HandHeldLegend/progcc-4-hw/3D/PCB/PGS_USBW_Board.step

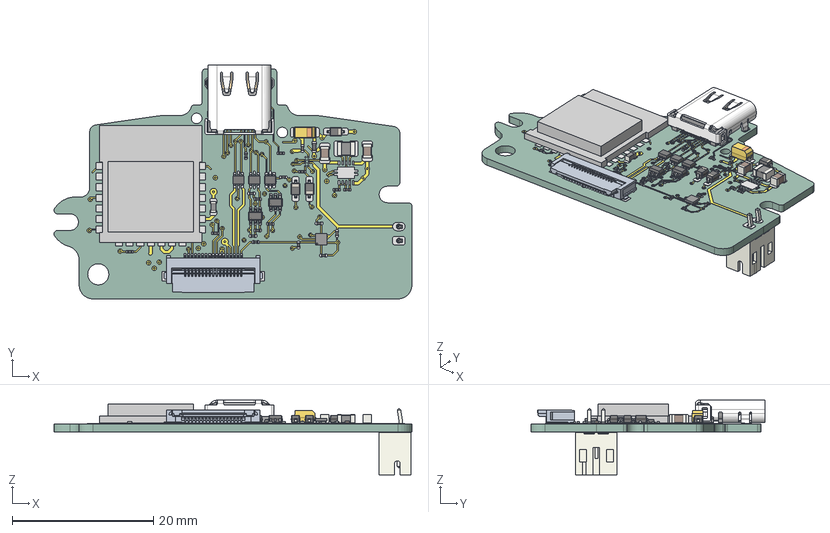
[picture p15: CAD file, 2026-09-22]
3D/PCB/PGS_USBW_Board.step
50.8 x 33.2 x 10.6 mm
R_0201_0603Metric x 15
RM2-Primitive v1
SOT-363_SC-70-6 x 2
L_0603_1608Metric
C_0805_2012Metric x 2
D_SOD-323 x 3
SOT_666 x 3
C_0201_0603Metric x 4
R_0402_1005Metric
L_1008_2520Metric
CP_EIA_3216_18_Kemet_A
JST_B2B_PH_K
PGS_USBW_Board_copper
PGS_USBW_Board_pad
PGS_USBW_Board_via
PGS_USBW_Board_PCB
