HandHeldLegend/progcc-4-hw/3D/STEP/Silicone DPad.step

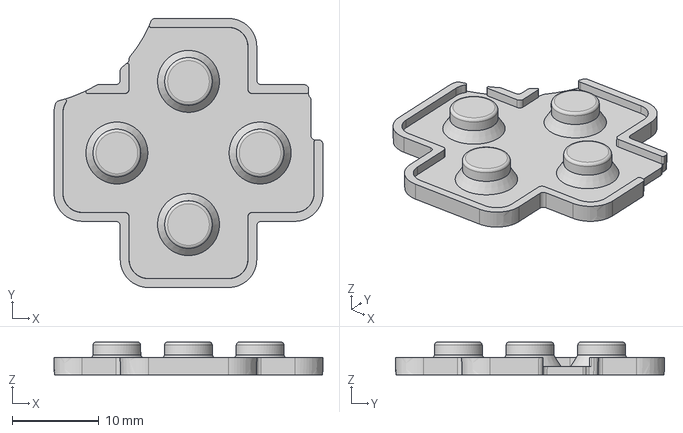
[picture p16: CAD file, 2026-09-22]
3D/STEP/Silicone DPad.step
31.0 x 31.0 x 3.80 mm
