HandHeldLegend/progcc-4-hw/3D/STL/DPad Body.stl

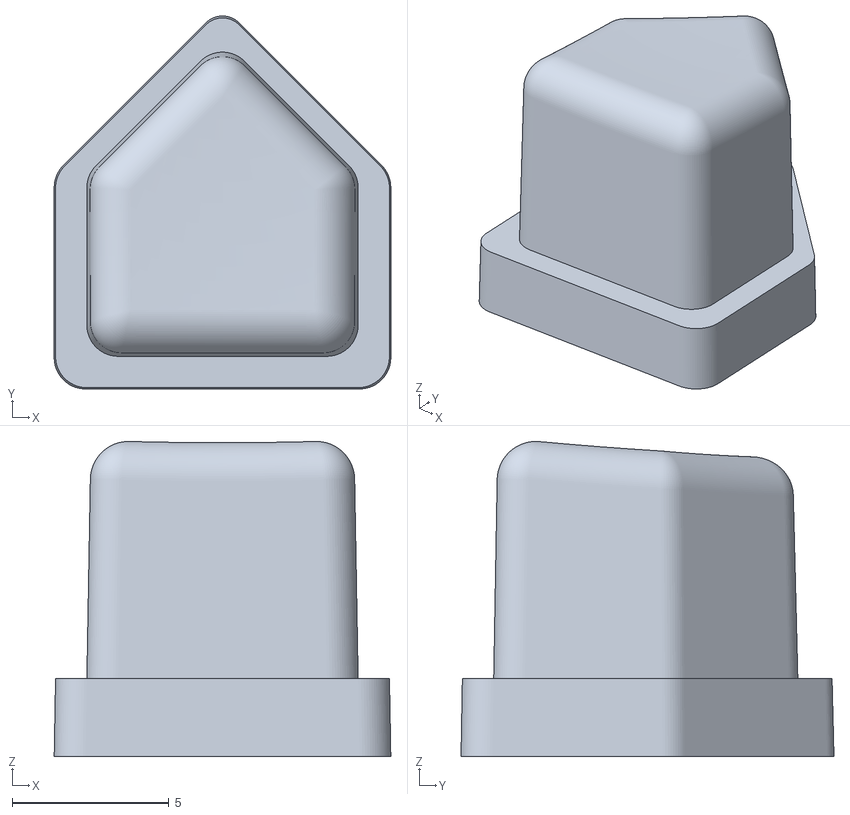
[picture p17: CAD file, 2026-09-25]
3D/STL/DPad Body.stl
10.8 x 11.9 x 10.1
