HandHeldLegend/progcc-4-hw/3D/STL/Button East Body.stl

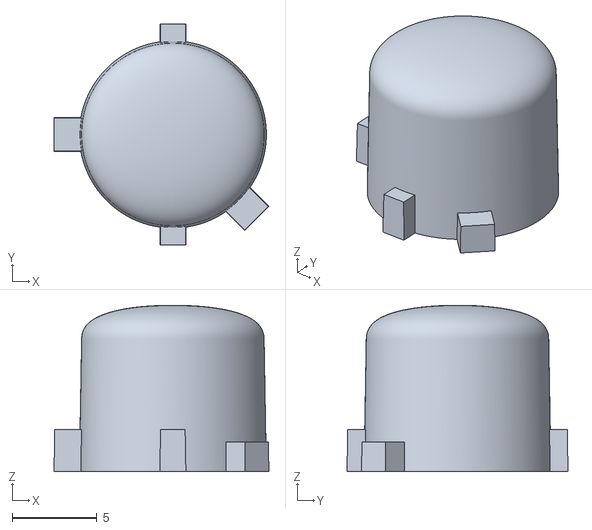
[picture p18: CAD file, 2026-09-25]
3D/STL/Button East Body.stl
12.7 x 13.0 x 9.82
