HandHeldLegend/progcc-4-hw/3D/STL/Triggers Body.stl

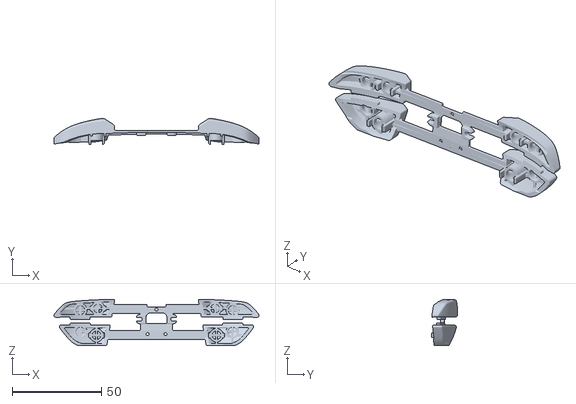
[picture p19: CAD file, 2026-09-25]
3D/STL/Triggers Body.stl
114.9 x 14.7 x 26.0
