HandHeldLegend/progcc-4-hw/PCB/Outlines/Trigger_Board_Export.dxf

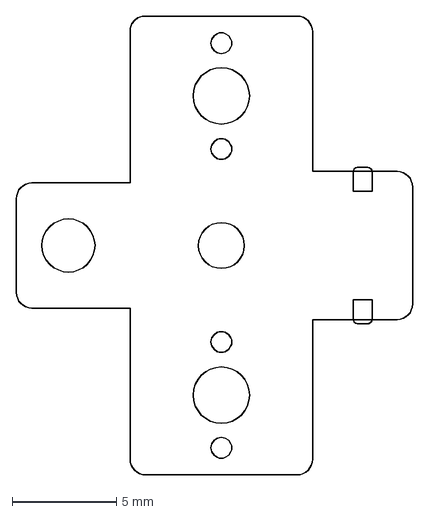
[picture p20: CAD file, 2025-05-15]
PCB/Outlines/Trigger_Board_Export.dxf
19.0 x 22.0 mm
