HandHeldLegend/progcc-4-hw/3D/STL/Player Lightpipe.stl

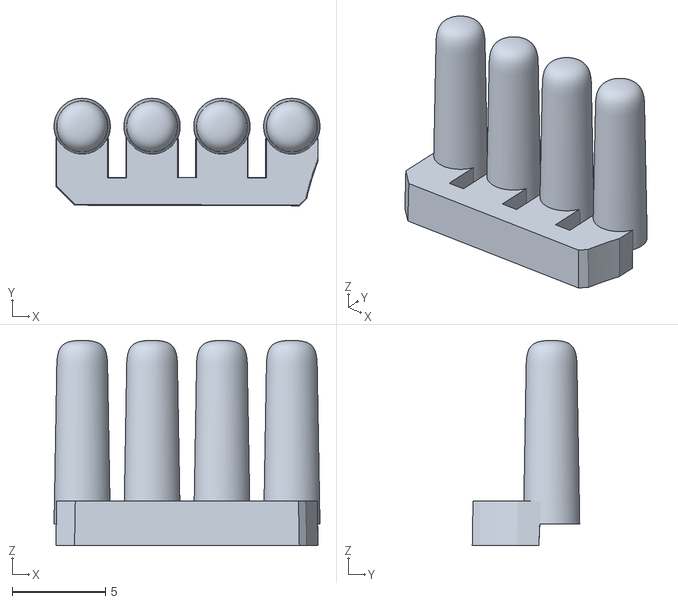
[picture p21: CAD file, 2026-09-22]
3D/STL/Player Lightpipe.stl
14.3 x 5.77 x 11.0
