HandHeldLegend/progcc-4-hw/PCB/Outlines/USB_Board_Export.dxf

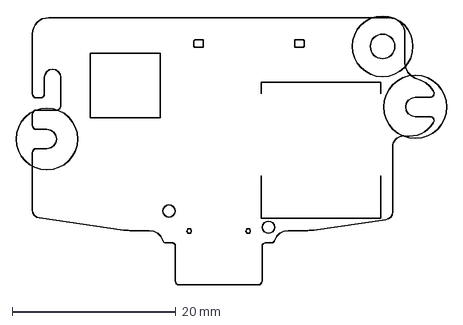
[picture p22: CAD file, 2025-05-15]
PCB/Outlines/USB_Board_Export.dxf
52.6 x 32.9 mm
