HandHeldLegend/progcc-4-hw/3D/STL/GL Button.stl

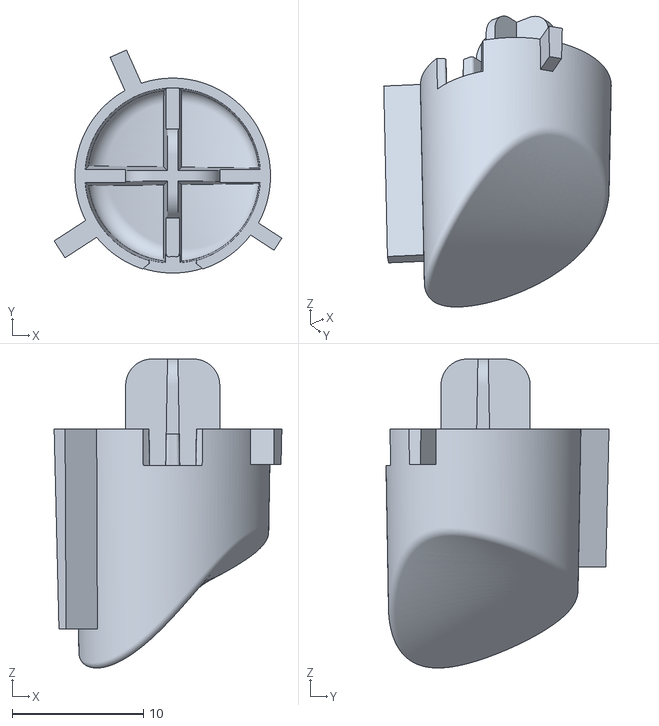
[picture p23: CAD file, 2026-09-22]
3D/STL/GL Button.stl
17.3 x 17.0 x 23.5
