HandHeldLegend/progcc-4-hw/PCB/Outlines/Stick_Module_Export.dxf

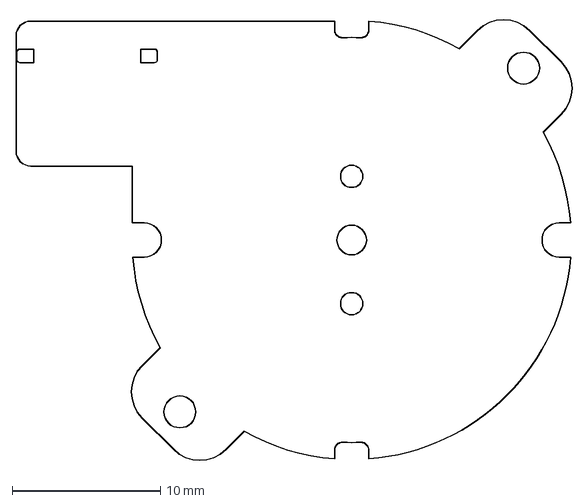
[picture p24: CAD file, 2025-05-15]
PCB/Outlines/Stick_Module_Export.dxf
37.5 x 30.2 mm
