HandHeldLegend/progcc-4-hw/3D/STL/Gateplate Round.stl

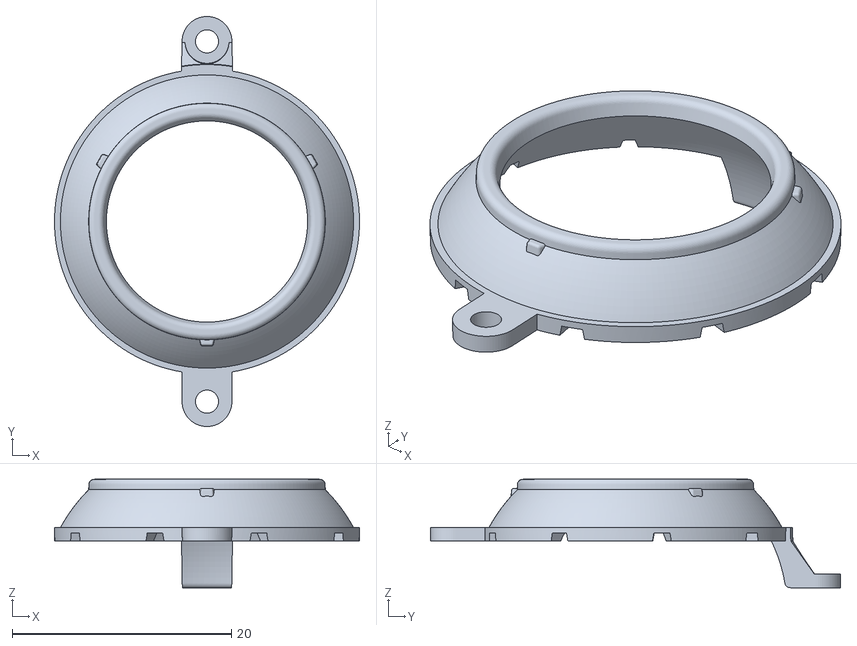
[picture p25: CAD file, 2026-09-22]
3D/STL/Gateplate Round.stl
27.8 x 37.4 x 9.89
