HandHeldLegend/progcc-4-hw/3D/STL/Shell Top Body.stl

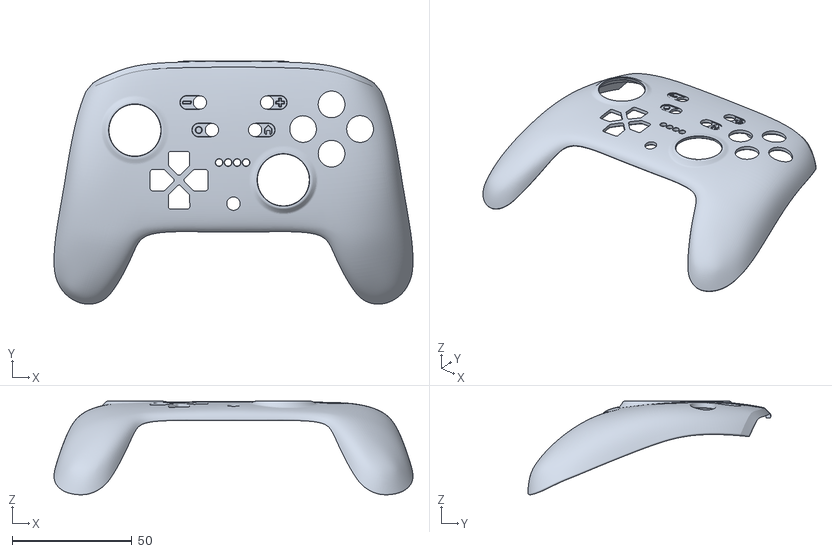
[picture p26: CAD file, 2026-09-22]
3D/STL/Shell Top Body.stl
150.0 x 101.7 x 39.1
