HandHeldLegend/progcc-4-hw/3D/STL/Shell Middle Body.stl

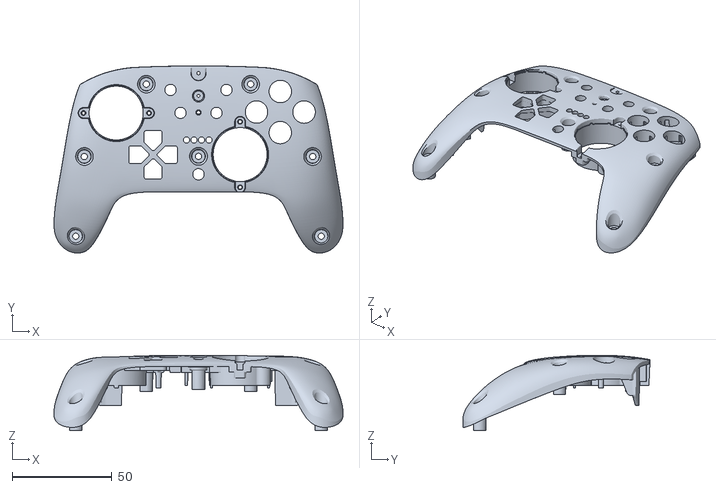
[picture p27: CAD file, 2026-09-22]
3D/STL/Shell Middle Body.stl
144.8 x 93.8 x 37.8
