HandHeldLegend/progcc-4-hw/3D/STL/Power Button.stl

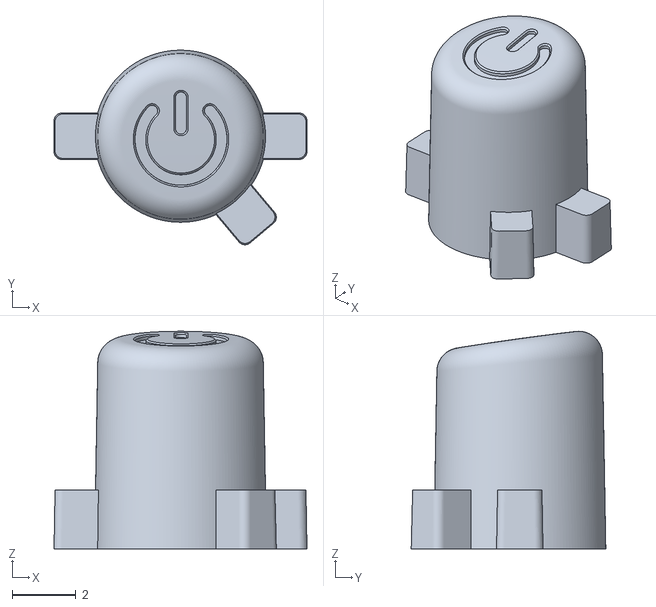
[picture p28: CAD file, 2026-09-22]
3D/STL/Power Button.stl
7.96 x 6.13 x 6.85
