HandHeldLegend/progcc-4-hw/3D/STL/Shell Lower Body.stl

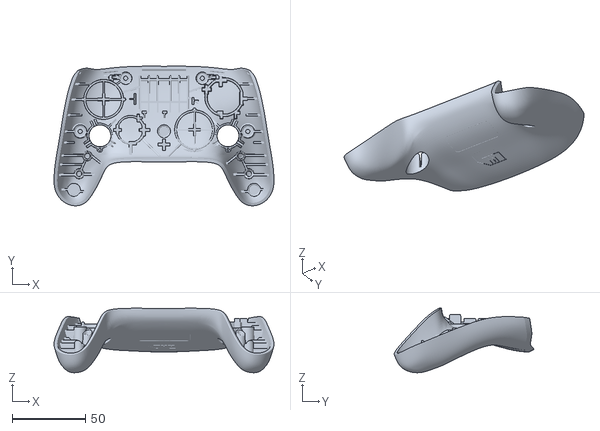
[picture p29: CAD file, 2026-09-22]
3D/STL/Shell Lower Body.stl
150.1 x 95.3 x 44.0
