HandHeldLegend/progcc-4-hw/3D/STL/Support Frame.stl

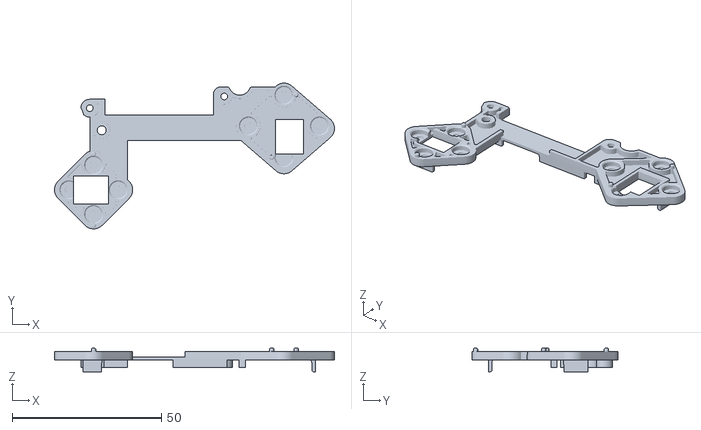
[picture p30: CAD file, 2026-09-22]
3D/STL/Support Frame.stl
93.7 x 48.8 x 7.89
