HandHeldLegend/progcc-4-hw/3D/STL/Menu Button.stl

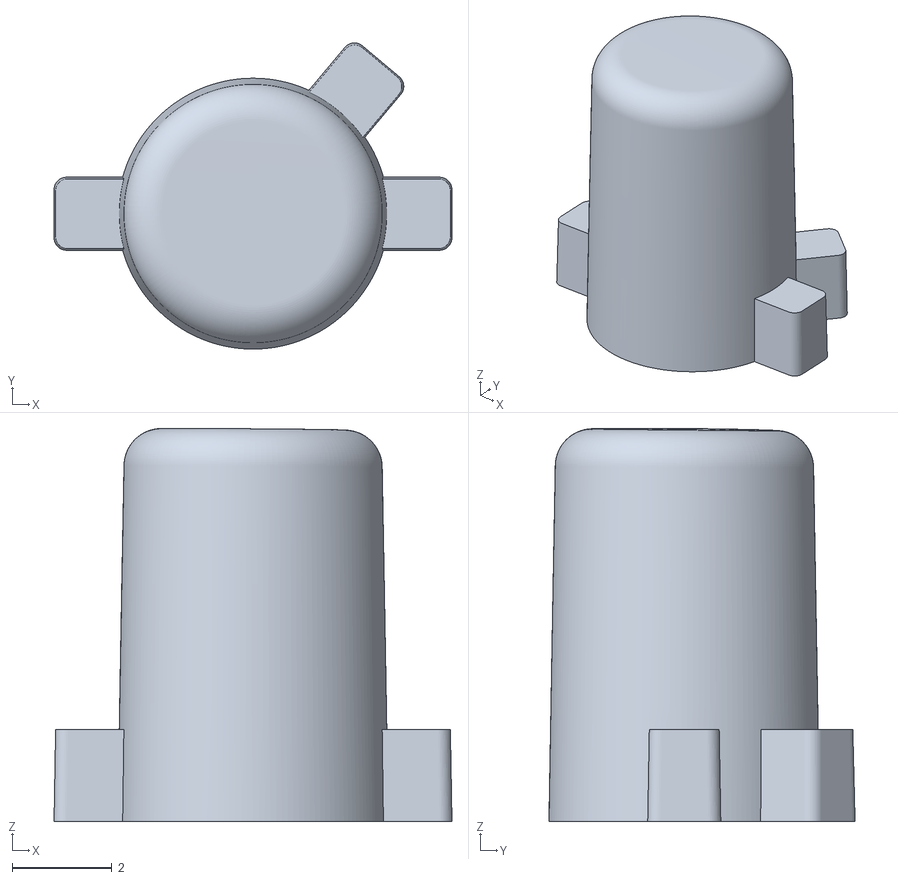
[picture p31: CAD file, 2026-09-22]
3D/STL/Menu Button.stl
7.96 x 6.13 x 7.87
