HandHeldLegend/progcc-4-hw/3D/STL/Trigger Bracket.stl

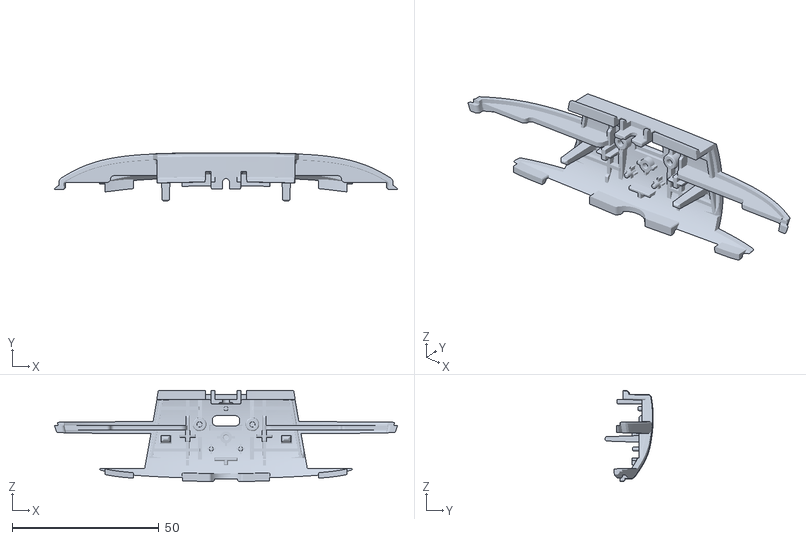
[picture p32: CAD file, 2026-09-22]
3D/STL/Trigger Bracket.stl
117.0 x 16.5 x 31.1
